etxmato/COMiX-HighSpeedDirectConnect/images/CHDC-Edge_Adapter_Slim.png

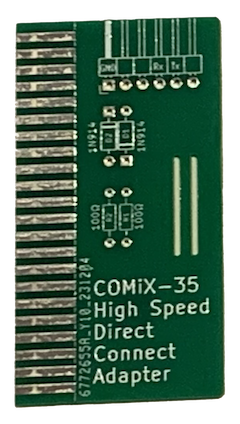
images/CHDC-Edge_Adapter_Slim.png
