etxmato/COMiX-HighSpeedDirectConnect/images/CHDC_Edge_Adapter.png

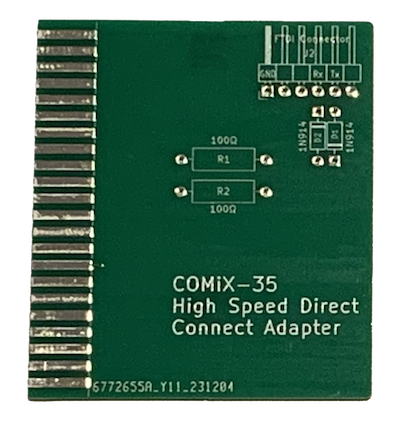
images/CHDC_Edge_Adapter.png
