etxmato/COMiX-HighSpeedDirectConnect/images/COMiX Direct Connect Edge Adapter Slim.png

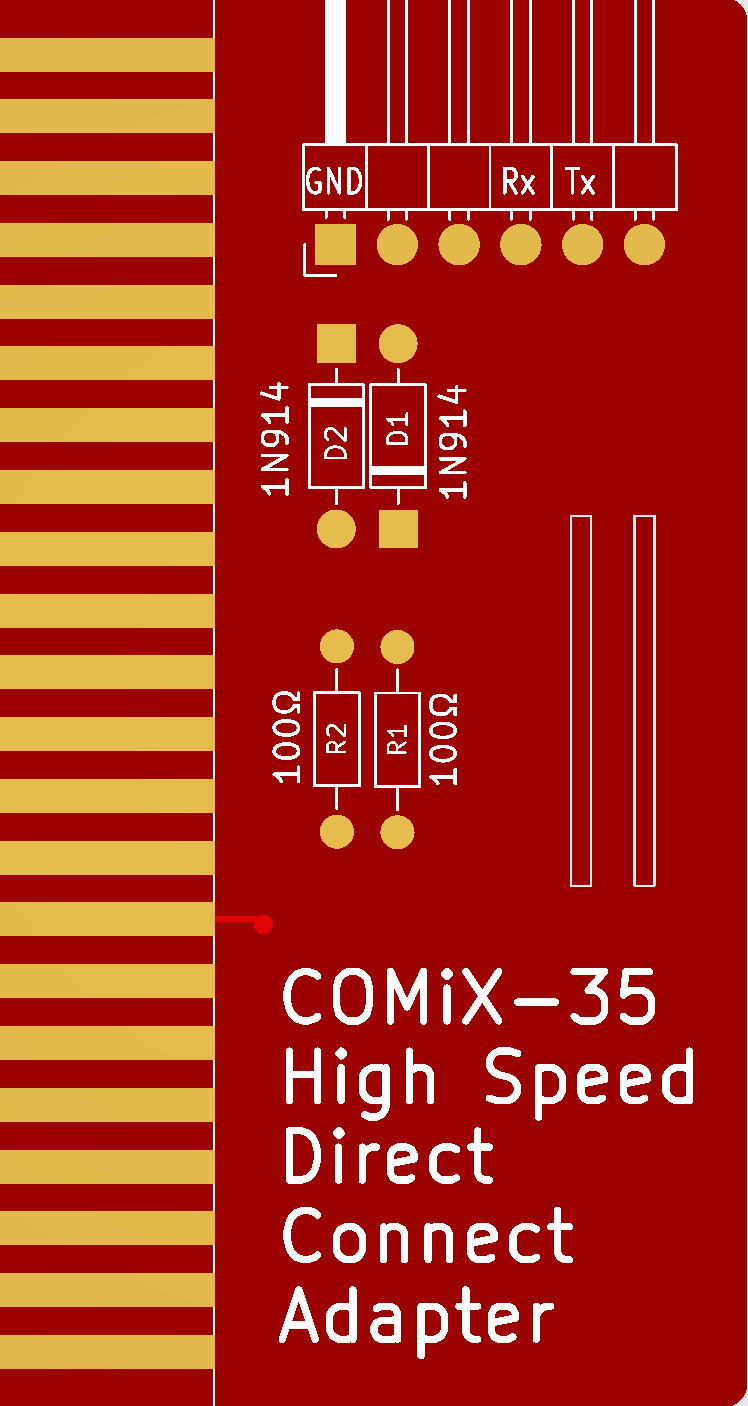
images/COMiX Direct Connect Edge Adapter Slim.png
