etxmato/COMiX-HighSpeedDirectConnect/images/COMiX-Edge-Connector-Smooth.png

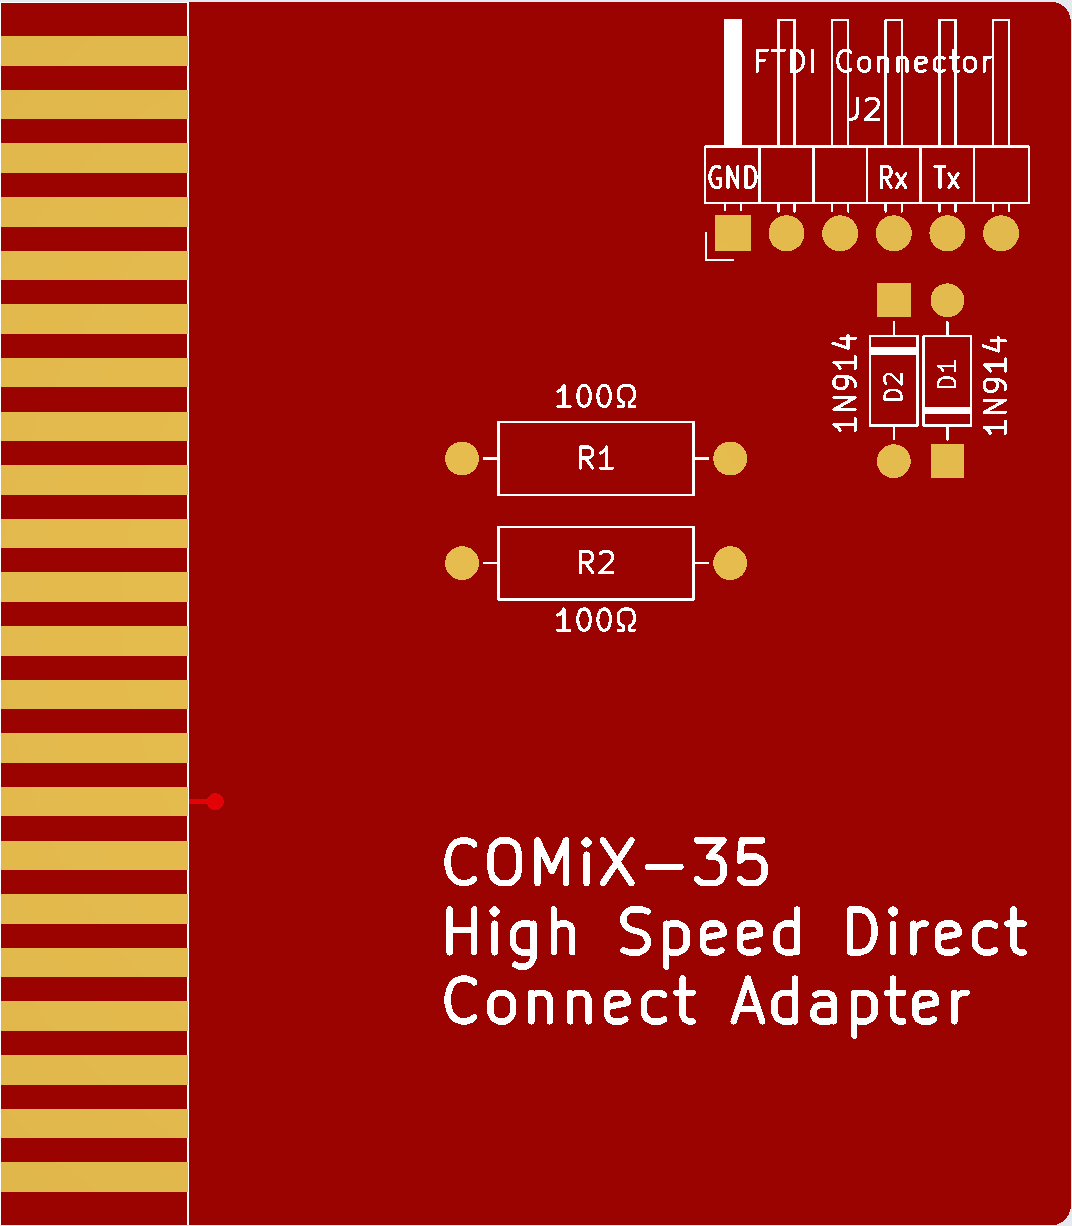
images/COMiX-Edge-Connector-Smooth.png
