etxmato/COMiX-HighSpeedDirectConnect/images/edge.png

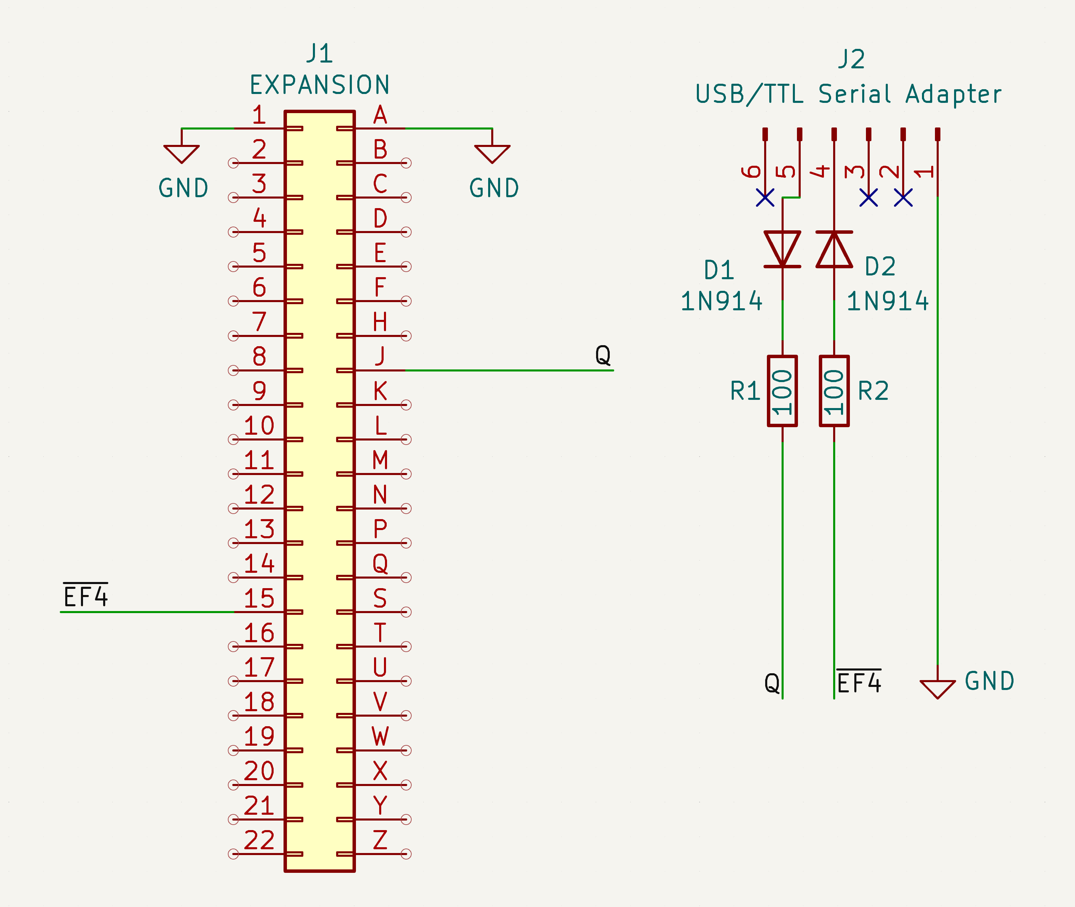
images/edge.png
