etxmato/COMiX-HighSpeedDirectConnect/images/HSDC Adapter Red.png

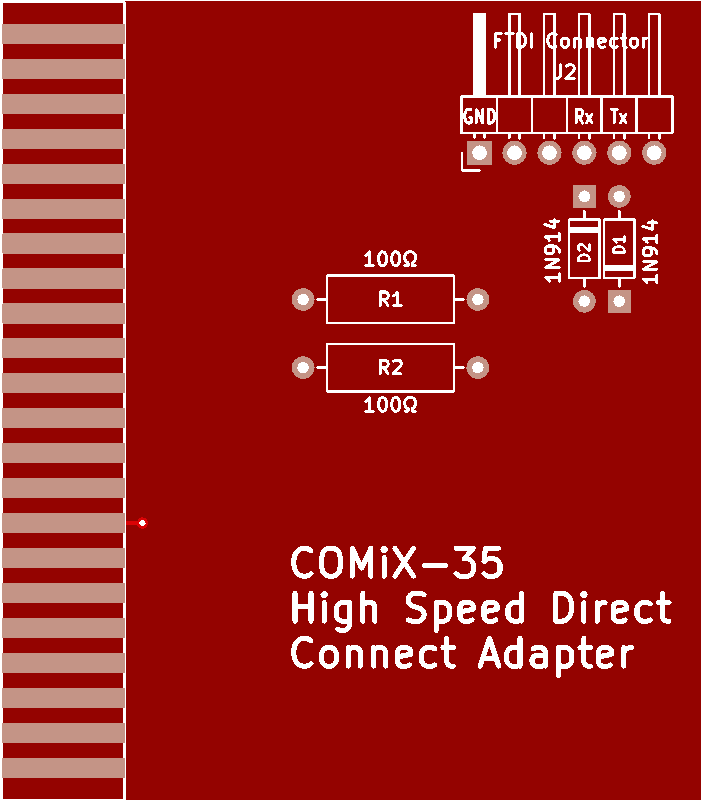
images/HSDC Adapter Red.png
