etxmato/COMiX-HighSpeedDirectConnect/images/HSDC Adapter.png

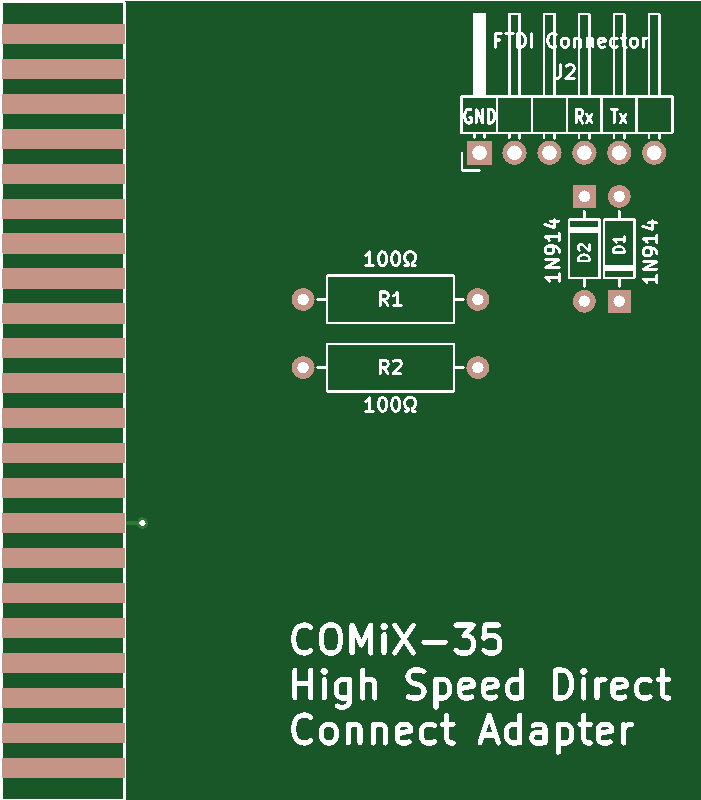
images/HSDC Adapter.png
