etxmato/COMiX-HighSpeedDirectConnect/images/HSDC Slim Adapter E.jpg

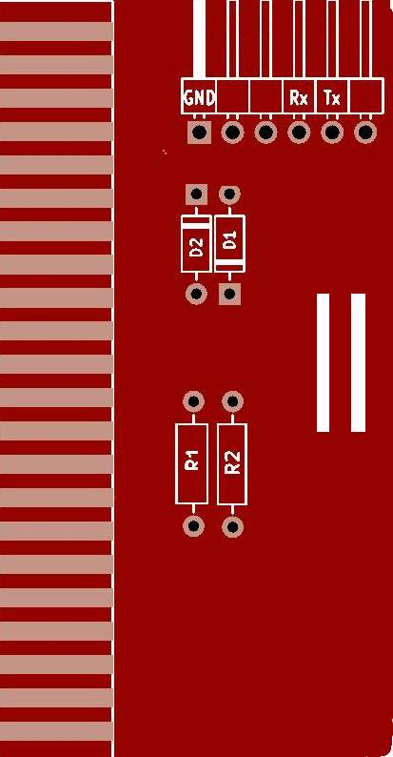
images/HSDC Slim Adapter E.jpg
