etxmato/COMiX-HighSpeedDirectConnect/images/IMG_9994.jpeg

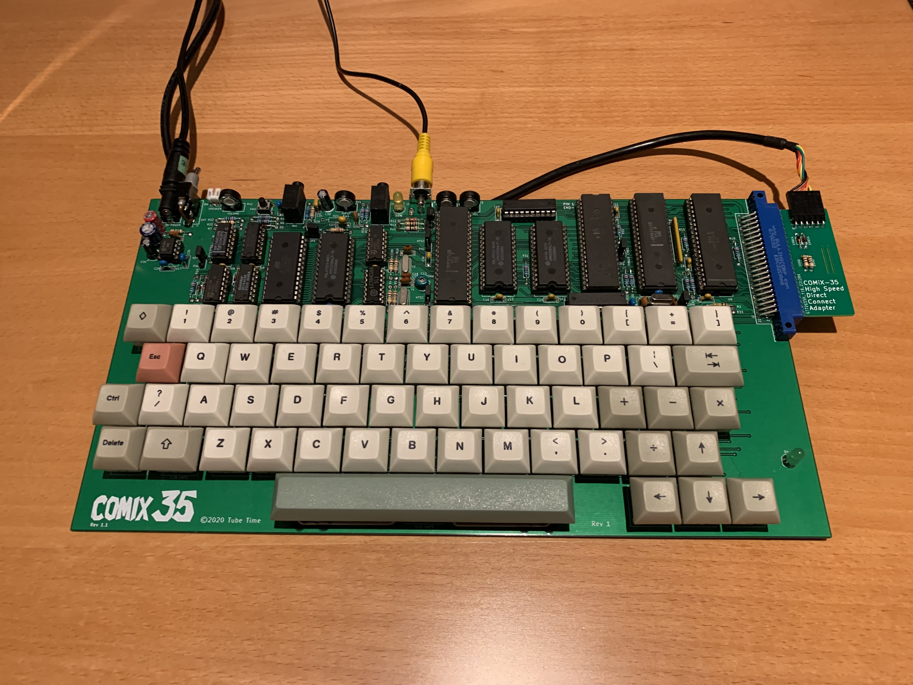
images/IMG_9994.jpeg
