etxmato/COMiX-HighSpeedDirectConnect/images/teraterm save file (logging) in preparation for COMiX PSAVE.jpg

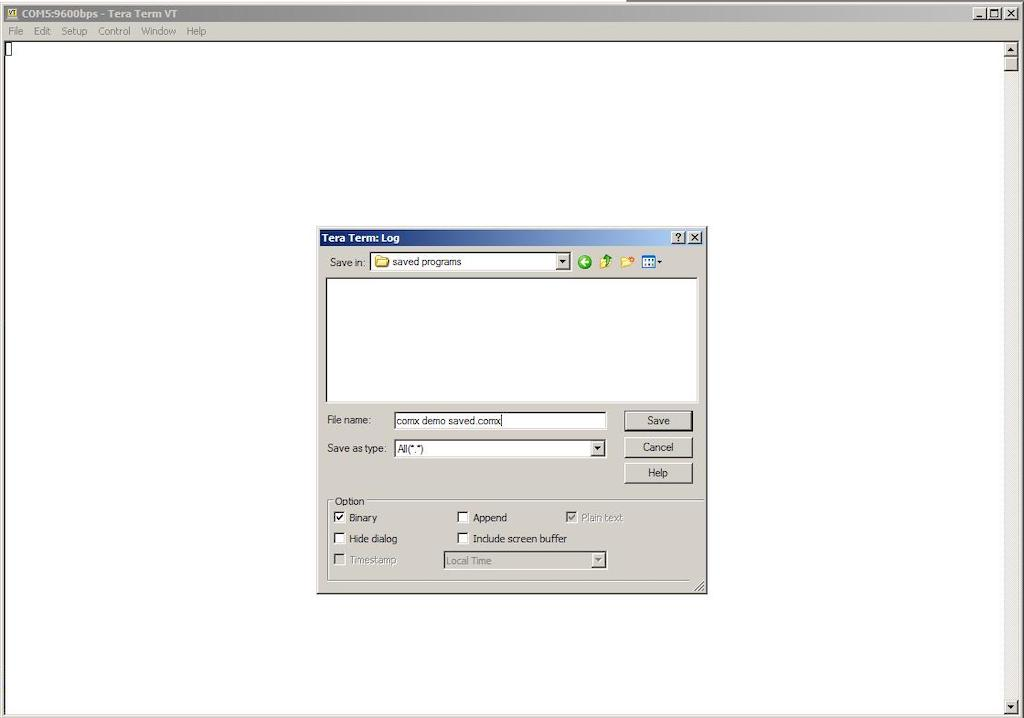
images/teraterm save file (logging) in preparation for COMiX PSAVE.jpg
