etxmato/COMiX-HighSpeedDirectConnect/images/Teraterm Serial Port Setup.jpg

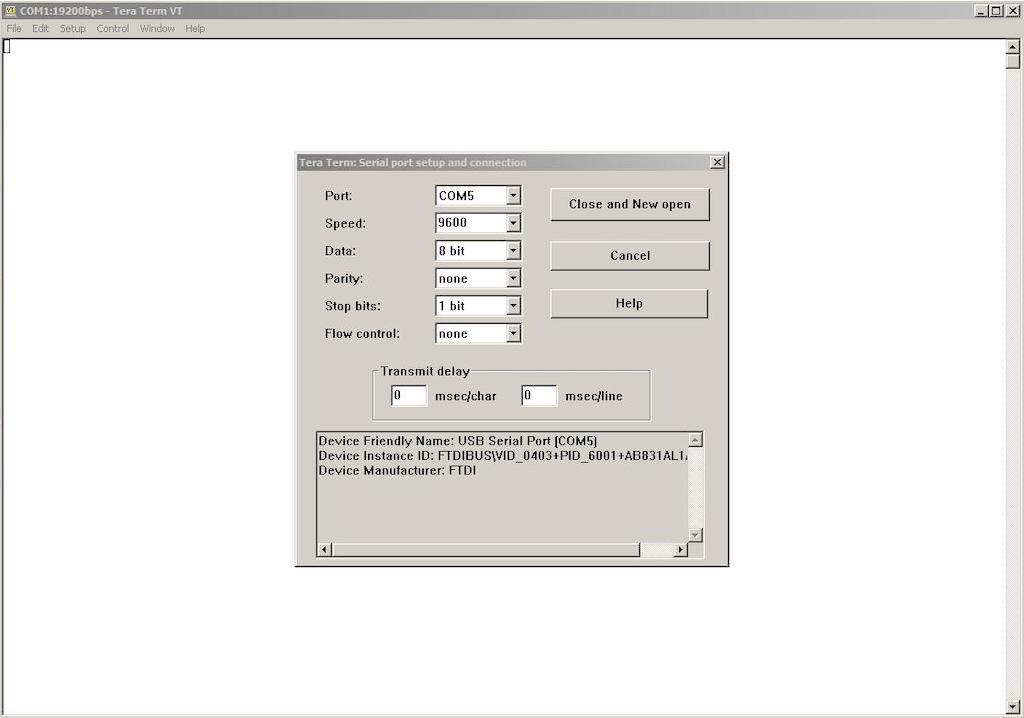
images/Teraterm Serial Port Setup.jpg
